herrkami/f-91ksd/fw/common/svc/svc.h

#pragma once

#include "util.h"
#include "lcd.h"
#include "main.h"
#include "menu.h"
#include "battery.h"
#include "leds.h"
#include "pulsar.h"
#include "beep.h"
#include "melody.h"
#include "chro.h"
#include "alarm.h"
#include "countdown.h"
#include "backlight.h"
#include "init.h"
// #include "otp.h"
#include "seconds_since_last_set.h"
#include "rtc_adj.h"
// #include "compass.h"
