herrkami/f-91ksd/fw/common/svc/countdown.c

#include "countdown.h"
#include "melody.h"
#include "pulsar.h"
#include "lcd.h"
#include "common/hal/hal.h"
#include "common/hal/lcd_segments.h"
#include <string.h>
#include "platform.h"

typedef struct {
	SVC_COUNTDOWN_COMMON
	int8_t sh;
	int8_t sm;
	int8_t ss;
} svc_countdown_priv_t;

static svc_countdown_priv_t SECTION_INFOMEM svc_countdowns[SVC_COUNTDOWN_NR];

#define NO_COUNTDOWN_PENDING 0xff

static uint8_t countdown_pending = NO_COUNTDOWN_PENDING;

static uint16_t countdowns_running = 0;

const uint8_t svc_countdowns_n = SVC_COUNTDOWN_NR;

void svc_countdown_init(void) {
	for(uint8_t i=0; i<svc_countdowns_n; i++) {
		svc_countdowns[i].melody = svc_default_melody_get();
		svc_countdowns[i].pulsar = svc_default_pulsar_get();
		svc_countdowns[i].successor = SVC_COUNTDOWN_SUCCESSOR_NONE;
	}
	svc_countdown_set_time(0, 0, 1, 0);
	svc_countdown_set_time(1, 0, 2, 0);
	svc_countdown_set_time(2, 0, 3, 0);
	svc_countdown_set_time(3, 0, 5, 0);
	svc_countdown_set_time(4, 0, 10, 0);
	svc_countdown_set_time(5, 0, 15, 0);
	svc_countdown_set_time(6, 0, 20, 0);
	svc_countdown_set_time(7, 0, 30, 0);
	svc_countdown_set_time(8, 0, 40, 0);
	svc_countdown_set_time(9, 1, 0, 0);
	svc_countdown_set_time(10, 2, 0, 0);
}

void svc_countdown_get(uint8_t index, svc_countdown_t *out) {
	memcpy(out, &(svc_countdowns[index]), sizeof(svc_countdown_t));
}

void svc_countdown_set_time(uint8_t index, uint8_t h, uint8_t m, uint8_t s) {
	svc_countdowns[index].h = h;
	svc_countdowns[index].sh = h;
	svc_countdowns[index].m = m;
	svc_countdowns[index].sm = m;
	svc_countdowns[index].s = s;
	svc_countdowns[index].ss = s;
}

// static void _svc_countdown_stop(svc_countdown_priv_t *cd) {
// 	cd->state = SVC_COUNTDOWN_STATE_STOP;
// 	cd->h = cd->sh;
// 	cd->m = cd->sm;
// 	cd->s = cd->ss;
// 	if(countdowns_running) {
// 		countdowns_running--;
// 	}
// }

void svc_countdown_stop(uint8_t index) {
	// _svc_countdown_stop(&(svc_countdowns[index]));
	svc_countdowns[index].state = SVC_COUNTDOWN_STATE_STOP;
	svc_countdowns[index].h = svc_countdowns[index].sh;
	svc_countdowns[index].m = svc_countdowns[index].sm;
	svc_countdowns[index].s = svc_countdowns[index].ss;
	countdowns_running &= ~(1<<index);
}

void svc_countdown_start(uint8_t index) {
	if(svc_countdowns[index].state != SVC_COUNTDOWN_STATE_PAUSE) {
		// countdowns_running++;
		countdowns_running |= (1<<index);
	}
	svc_countdowns[index].state = SVC_COUNTDOWN_STATE_RUN;
}

static void _svc_countdown_pause(uint8_t index) {
	svc_countdowns[index].state = SVC_COUNTDOWN_STATE_PAUSE;
}

void svc_countdown_play_pause(uint8_t index) {
	if(svc_countdowns[index].state == SVC_COUNTDOWN_STATE_RUN) {
		_svc_countdown_pause(index);
	}
	else if(svc_countdowns[index].state == SVC_COUNTDOWN_STATE_PAUSE) {
		svc_countdown_start(index);
	}
}

// static uint8_t svc_countdown_dec(svc_countdown_priv_t *cd) {
static uint8_t svc_countdown_dec(uint8_t index) {
	svc_countdown_priv_t *cd = &svc_countdowns[index];
	if(cd->state != SVC_COUNTDOWN_STATE_RUN) {
		return 0;
	}
	cd->s--;
	if(cd->s == -1) {
		cd->s = 59;
		cd->m--;
		if(cd->m == -1) {
			cd->m = 59;
			cd->h--;
			if(cd->h == -1) {
				svc_countdown_stop(index);
				return 1;
			}
		}
	}
	return 0;
}

void svc_countdown_process(void) {
	if(countdowns_running) {
		for(uint8_t i=0; i<svc_countdowns_n; i++) {
			// if(svc_countdown_dec(&(svc_countdowns[i]))) {
			if(svc_countdown_dec(i)) {
				// Make sure metronome is off
				svc_pulsar_bp_metronome_set_enable(svc_countdowns[i].metronome);
				svc_melody_play_repeat(
					svc_countdowns[i].melody, svc_melody_alarm_repetitions_get());
				svc_pulsar_play_repeat(
					svc_countdowns[i].pulsar, svc_pulsar_alarm_repetitions_get());

				countdown_pending = i;

				uint8_t successor = svc_countdowns[i].successor;
				if(successor != SVC_COUNTDOWN_SUCCESSOR_NONE) {
					svc_countdown_start(successor);
				}
			}
		}
	}
}

void svc_countdown_draw_popup(void) {
	static uint8_t div = 0;

	if(countdown_pending != NO_COUNTDOWN_PENDING) {
		if(div < 4) {
			hal_lcd_seg_set(HAL_LCD_SEG_COLON, 0);
			svc_lcd_puts(0, "ctdn");
			svc_lcd_puti(4, 2, countdown_pending);
			svc_lcd_force_redraw();
		}
	}
	div = (div+1)%8;
}

uint8_t svc_countdown_get_n_running(void) {
	uint8_t n_running = 0;
	for(uint8_t i = 0; i < SVC_COUNTDOWN_NR; i++) {
		n_running += !!(countdowns_running & (1 << i));
	}
	return n_running;
}

uint8_t svc_coundown_get_running(void) {
	return countdowns_running;
}

uint8_t svc_countdowns_are_running(void) {
	return !!countdowns_running;
}

uint8_t svc_countdown_get_pending(void) {
	return countdown_pending != NO_COUNTDOWN_PENDING;
}

void svc_countdown_clear_pending(void) {
	countdown_pending = NO_COUNTDOWN_PENDING;
}

void svc_countdown_set_melody(uint8_t index, uint8_t melody) {
	svc_countdowns[index].melody = melody;
}

void svc_countdown_set_pulsar(uint8_t index, uint8_t pulsar) {
	svc_countdowns[index].pulsar = pulsar;
}

void svc_countdown_set_successor(uint8_t index, uint8_t successor) {
	svc_countdowns[index].successor = successor;
}

void svc_countdown_set_metronome(uint8_t index, uint8_t state) {
	svc_countdowns[index].metronome = state;
}
